christoph1j2/ESP8266-Shield/dokumentace/fotky/20240805_180028.jpg

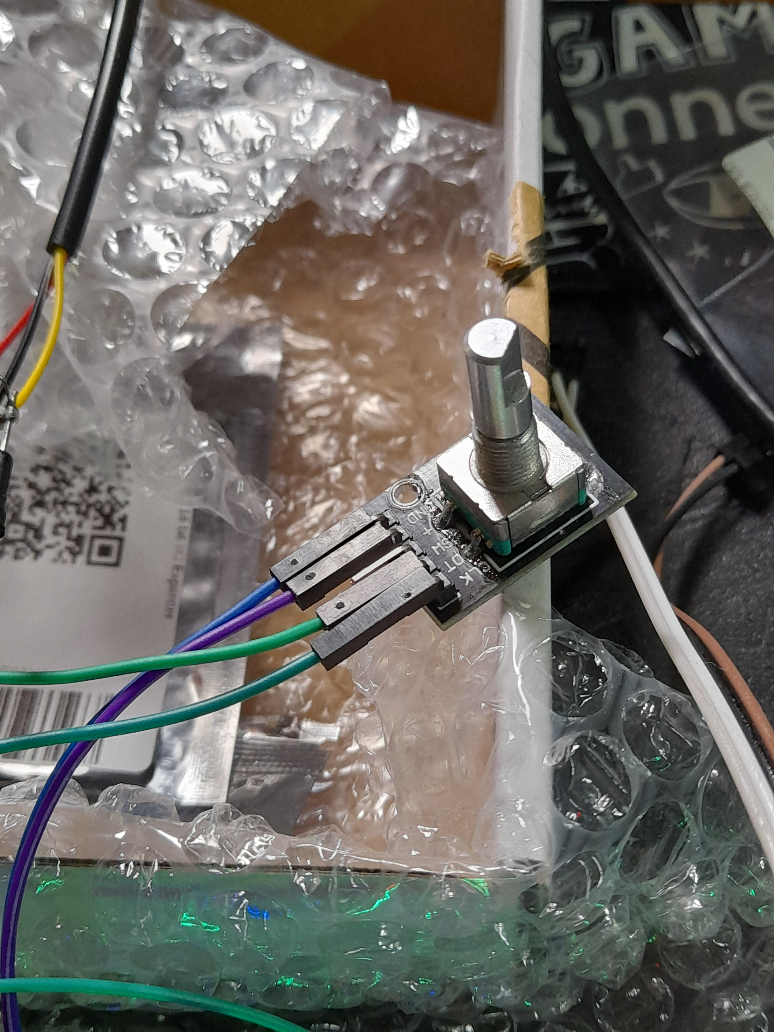
dokumentace/fotky/20240805_180028.jpg
