christoph1j2/ESP8266-Shield/dokumentace/fotky/Snapchat-1074486183.jpg

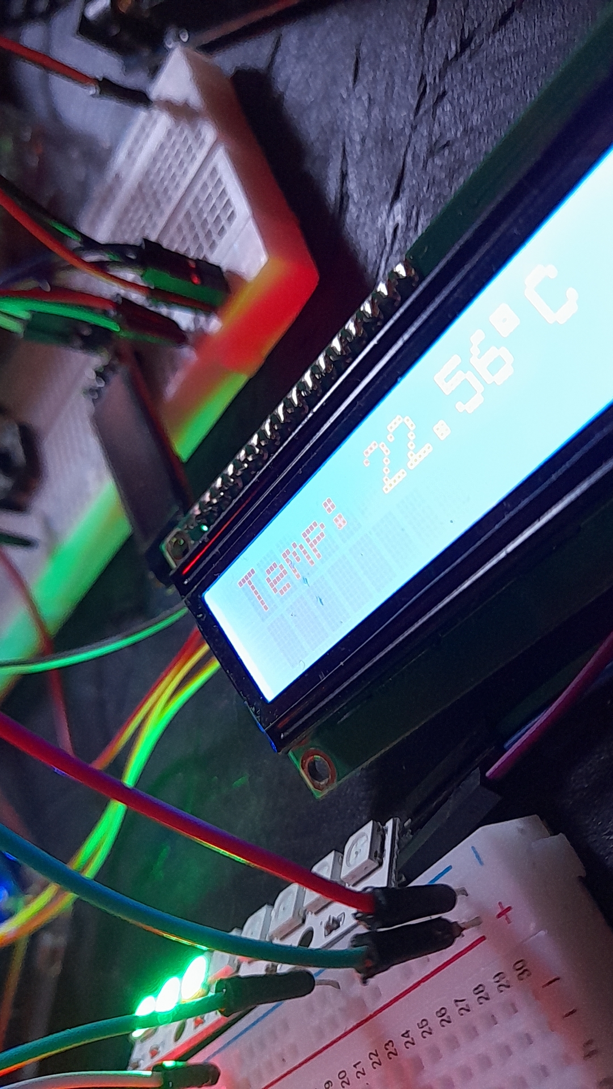
dokumentace/fotky/Snapchat-1074486183.jpg
