christoph1j2/ESP8266-Shield/soubory/ds18b20.jpg

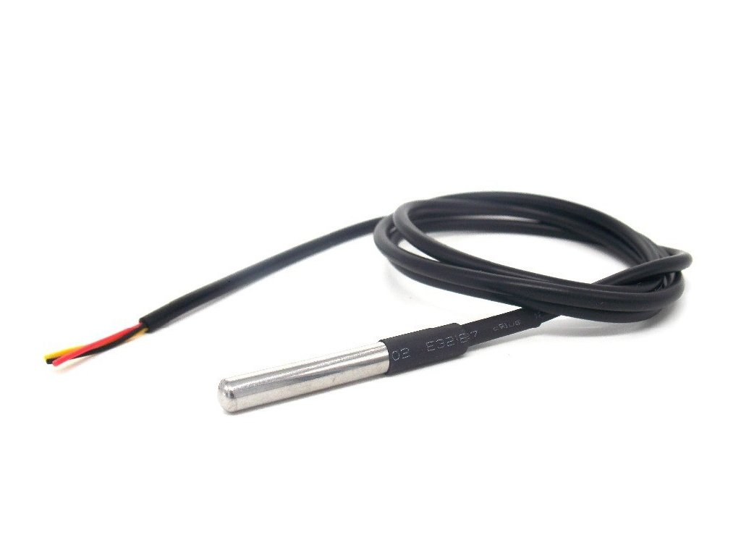
soubory/ds18b20.jpg
